telzo2000/cool644/firmware/qmk0.22/cool644/keymaps/vial/config.h

#pragma once
#define PIMORONI_TRACKBALL_SCALE 20

#define MASTER_RIGHT
#define POINTING_DEVICE_ROTATION_180

#define VIAL_KEYBOARD_UID {0xB5, 0xF4, 0x52, 0x68, 0x0C, 0x45, 0x35, 0x10}
#define VIAL_UNLOCK_COMBO_ROWS { 0, 1 }
#define VIAL_UNLOCK_COMBO_COLS { 0, 1 }
